avenqo/pong_32x32/doc/images/IMG_8806.jpg

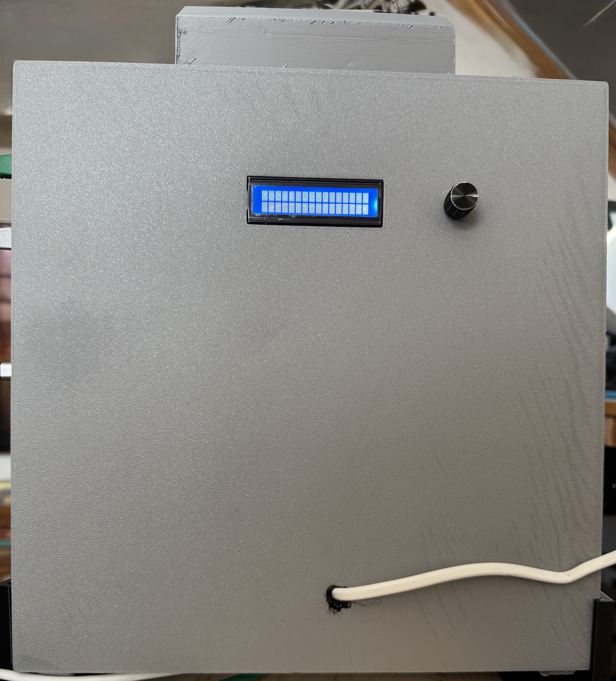
doc/images/IMG_8806.jpg
