avenqo/pong_32x32/doc/images/IMG_8807.jpg

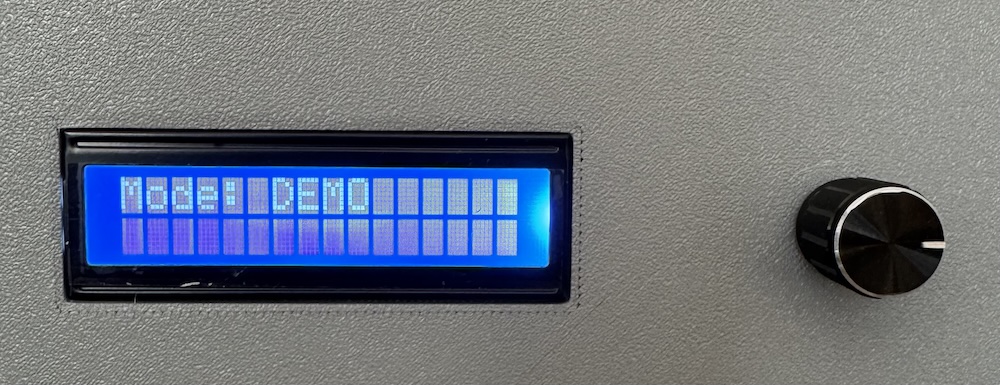
doc/images/IMG_8807.jpg
