avenqo/pong_32x32/doc/images/IMG_8813 4.jpg

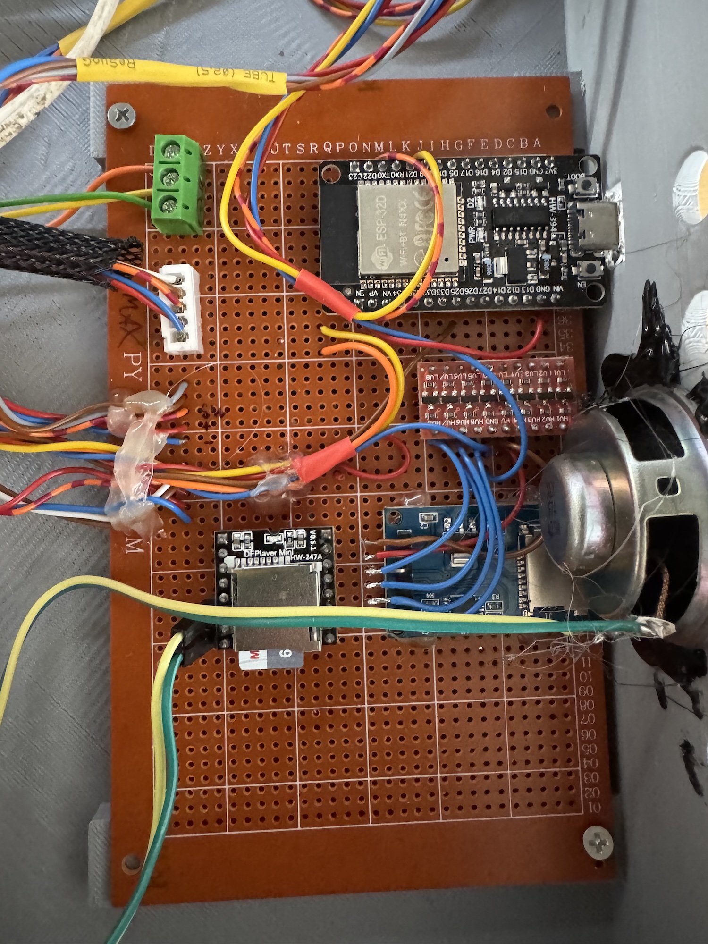
doc/images/IMG_8813 4.jpg
